EngThi/The-Nerve/assets/renders/Back_View.png

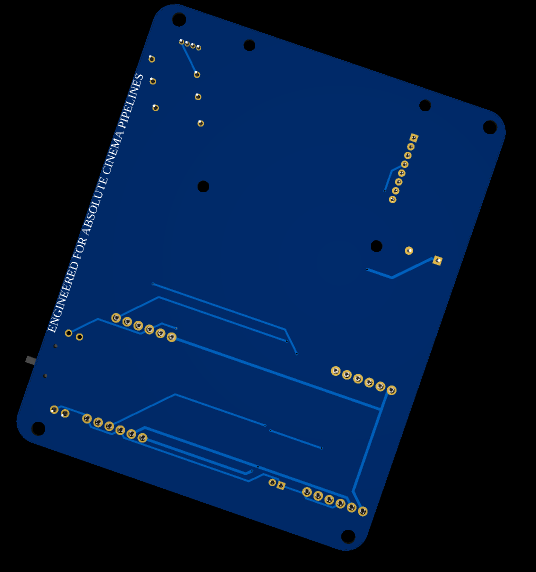
assets/renders/Back_View.png
