EngThi/The-Nerve/assets/renders/Frontal_View.png

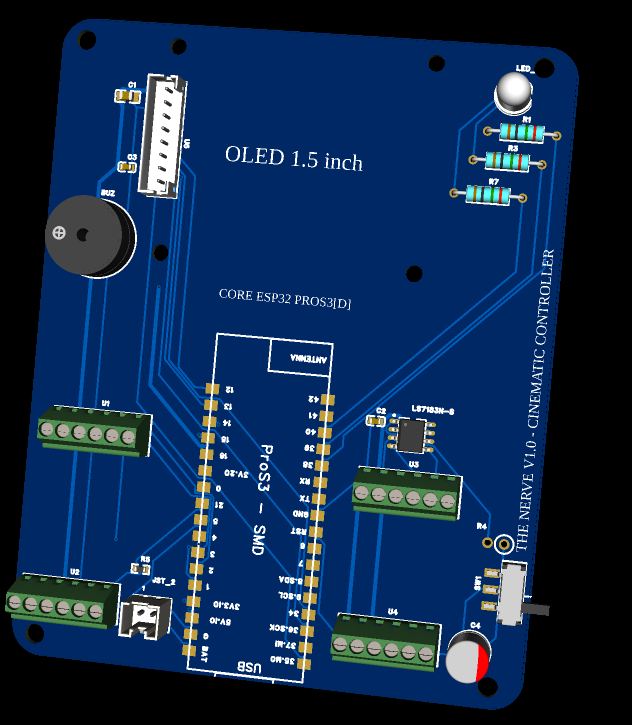
assets/renders/Frontal_View.png
