EngThi/The-Nerve/assets/renders/The Nerve 3D.png

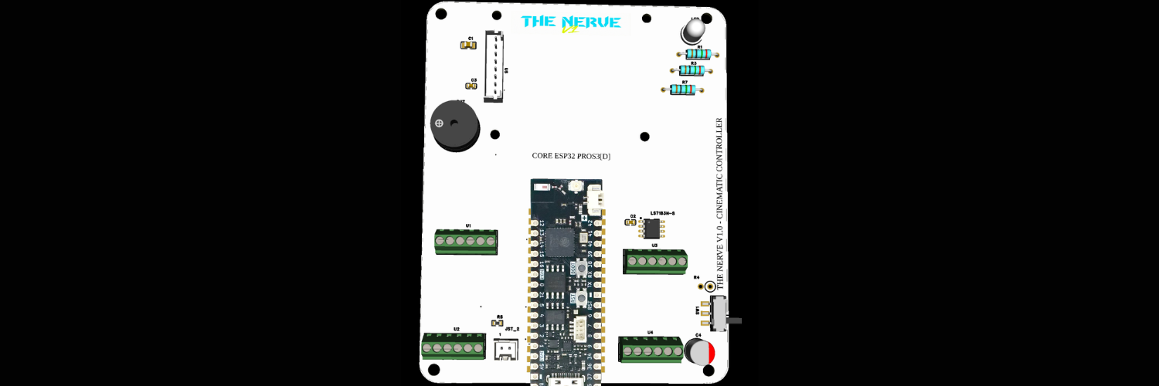
assets/renders/The Nerve 3D.png
