EngThi/The-Nerve/assets/renders/the_nerve_bottom_render.png

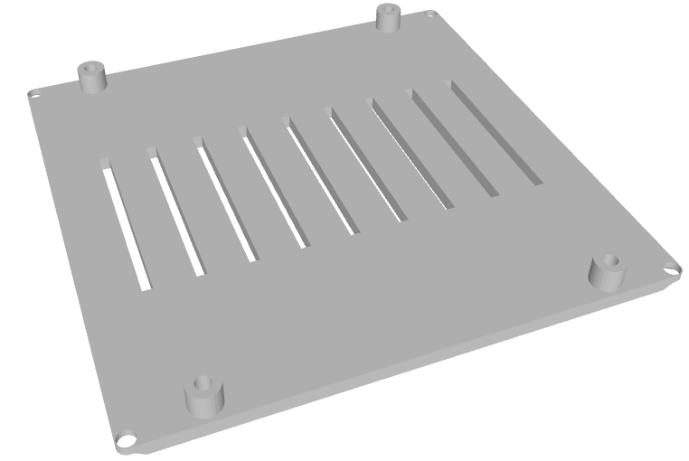
assets/renders/the_nerve_bottom_render.png
