EngThi/The-Nerve/assets/renders/the_nerve_full_enclosure_render.png

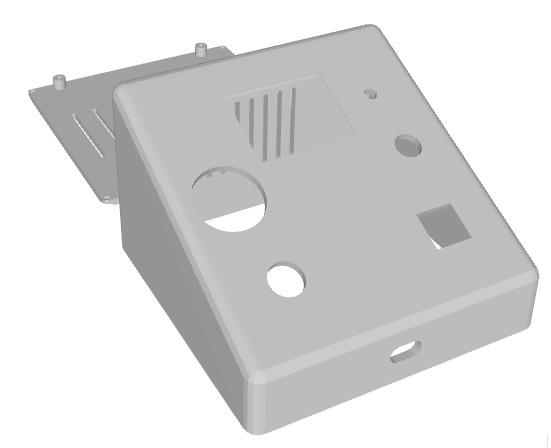
assets/renders/the_nerve_full_enclosure_render.png
