EngThi/The-Nerve/assets/renders/the_nerve_top_render.png

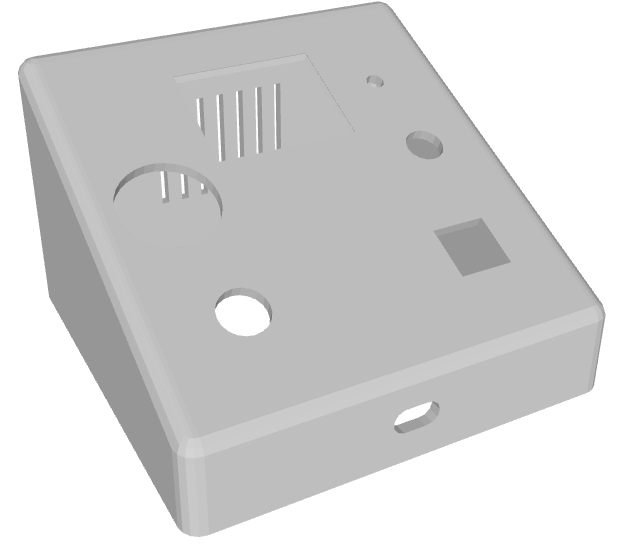
assets/renders/the_nerve_top_render.png
