EngThi/The-Nerve/assets/journal/JLCPCBshipmethods.png

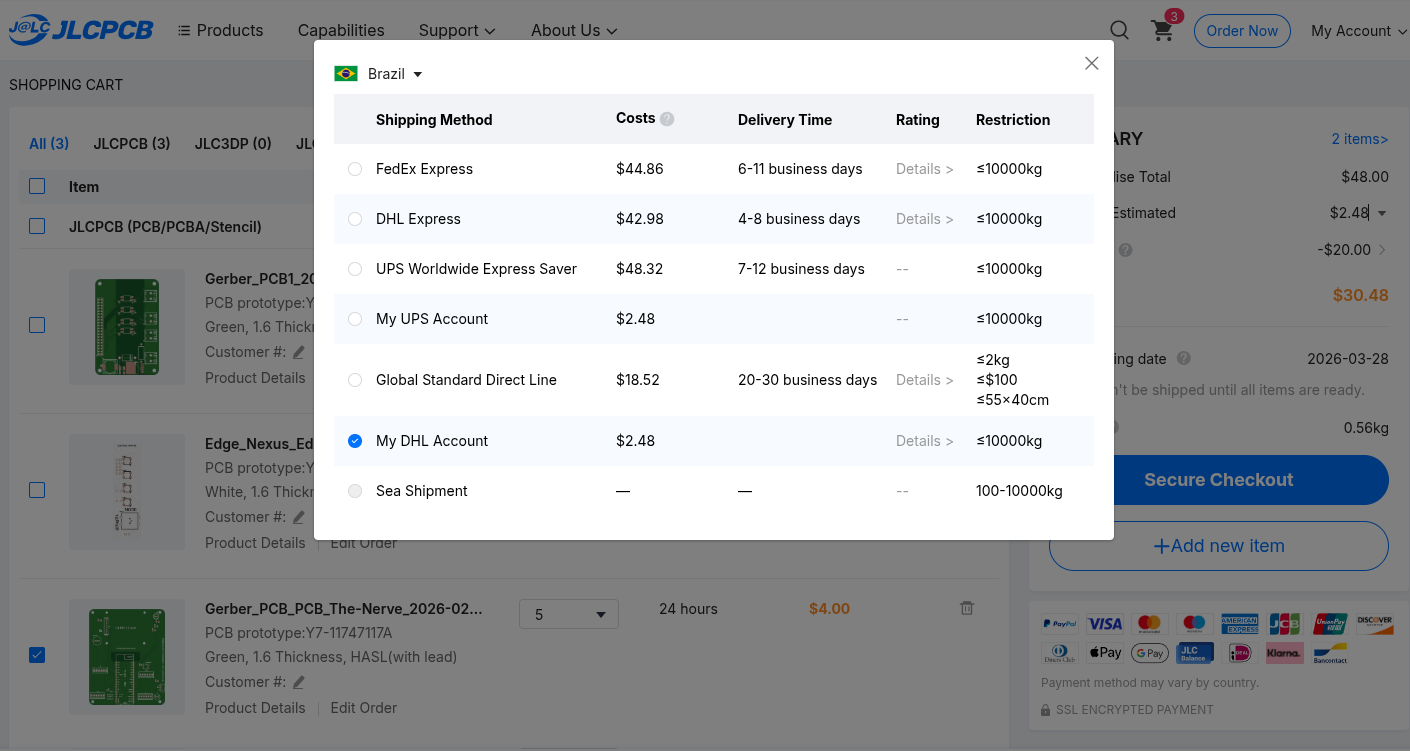
assets/journal/JLCPCBshipmethods.png
