EngThi/The-Nerve/assets/journal/Oled.png

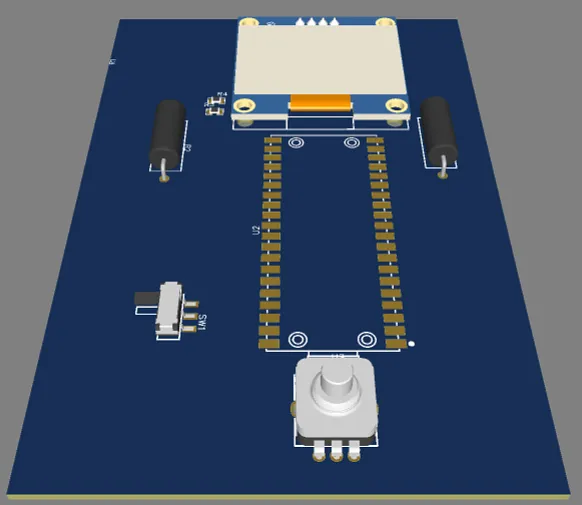
assets/journal/Oled.png
