EngThi/The-Nerve/assets/journal/PlacaJLC.png

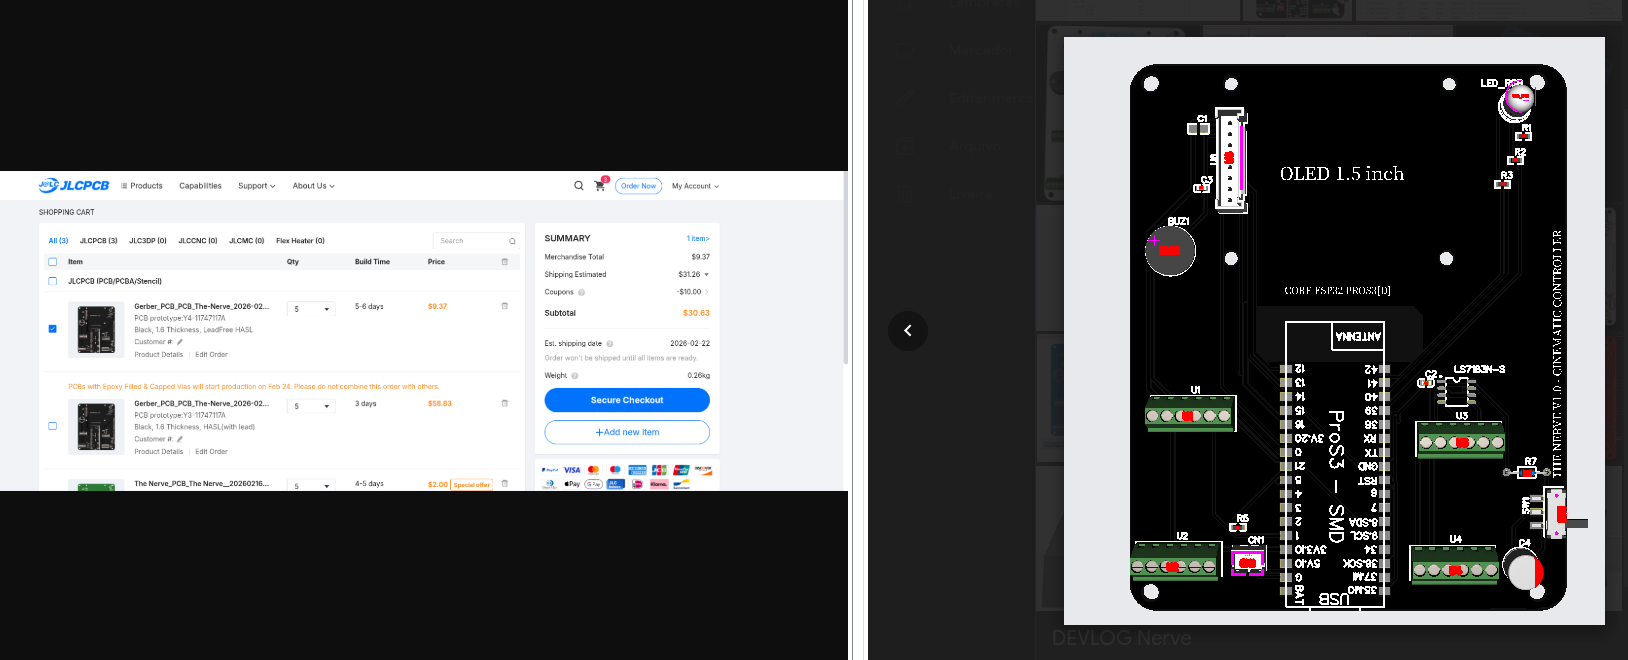
assets/journal/PlacaJLC.png
