EngThi/The-Nerve/assets/journal/Terminais.png

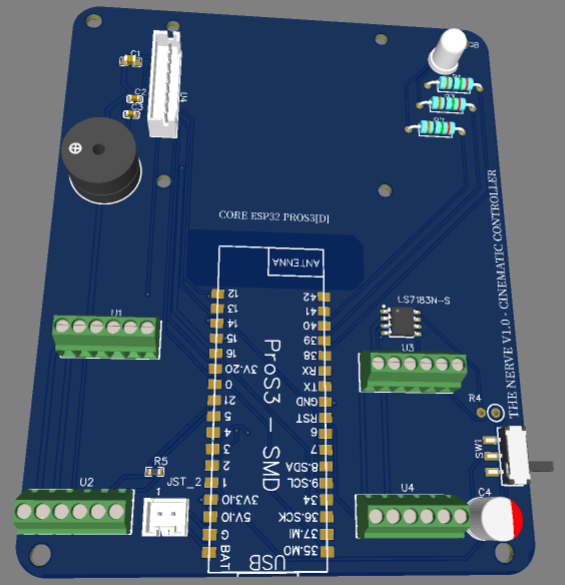
assets/journal/Terminais.png
